adotagarwal/WatchTower2/docs/PXL_20250728_205028200.jpg

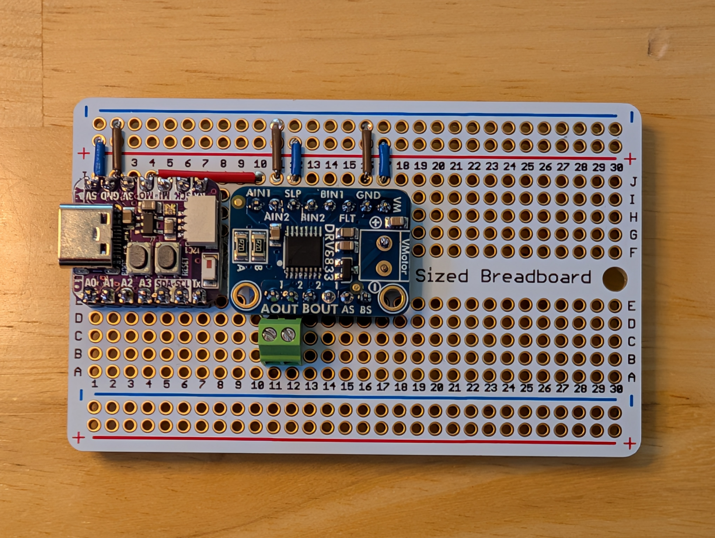
docs/PXL_20250728_205028200.jpg
